adamulrich/CulturalHallLighting/20211202_095547.jpg

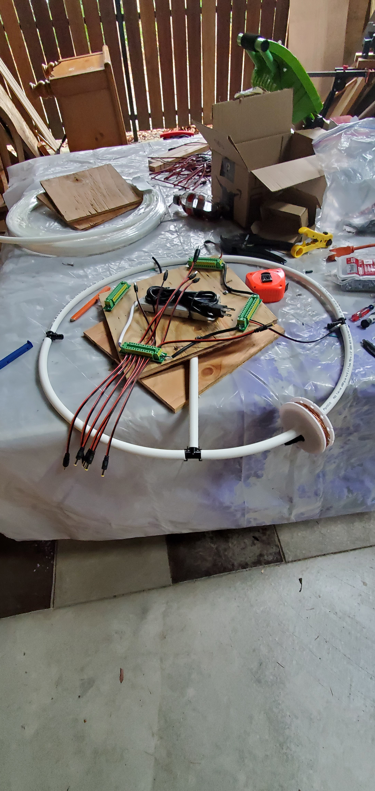
20211202_095547.jpg
