adamulrich/CulturalHallLighting/20211214_210018.jpg

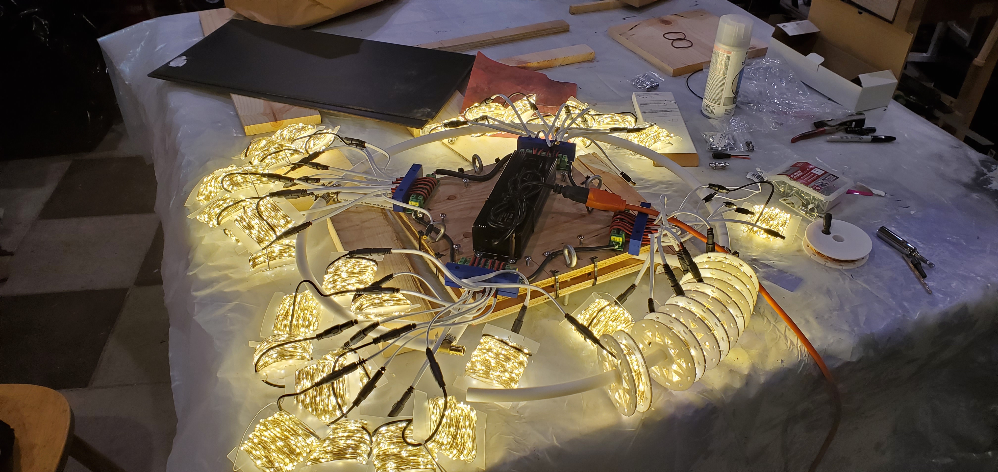
20211214_210018.jpg
