adamulrich/CulturalHallLighting/20211214_210051 (Large).jpg

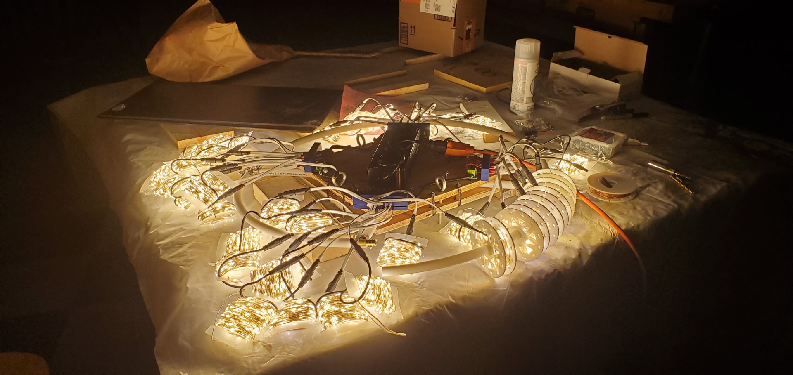
20211214_210051 (Large).jpg
