adamulrich/CulturalHallLighting/IMG_20211204_191200.jpg

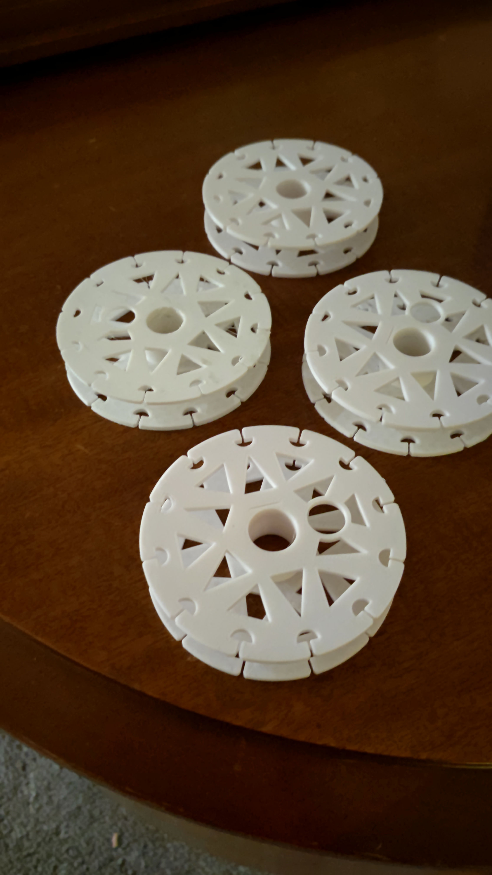
IMG_20211204_191200.jpg
