adamulrich/CulturalHallLighting/IMG_20211204_191239.jpg

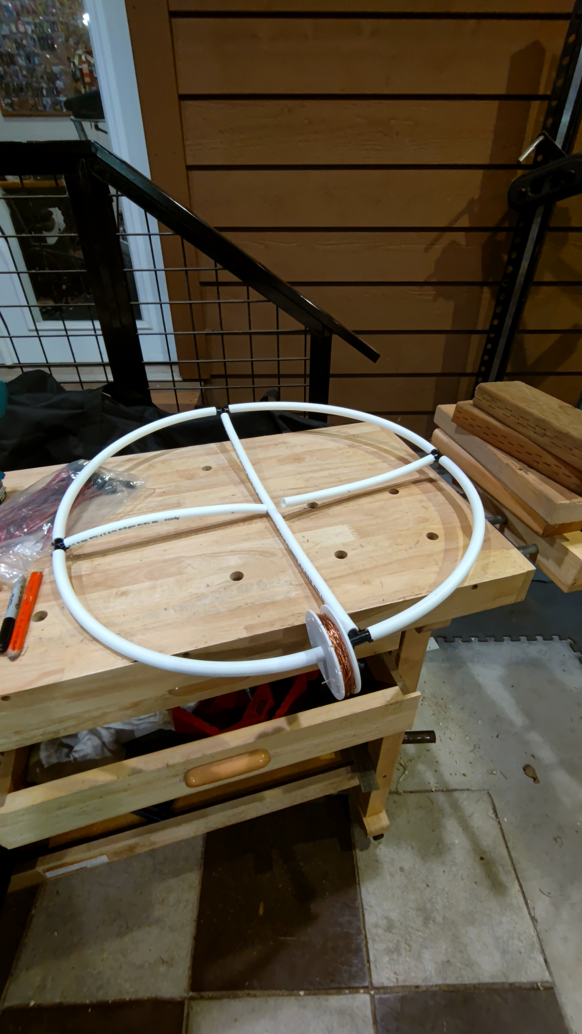
IMG_20211204_191239.jpg
