adamulrich/CulturalHallLighting/IMG_20211204_191243.jpg

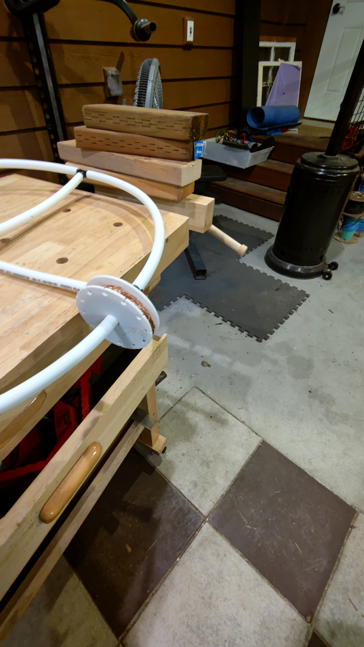
IMG_20211204_191243.jpg
