adamulrich/CulturalHallLighting/IMG_20211204_191250.jpg

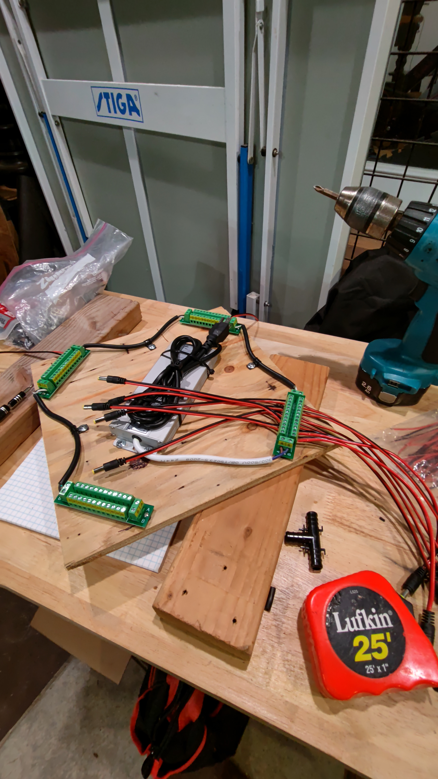
IMG_20211204_191250.jpg
