adamulrich/CulturalHallLighting/IMG_20211204_191428.jpg

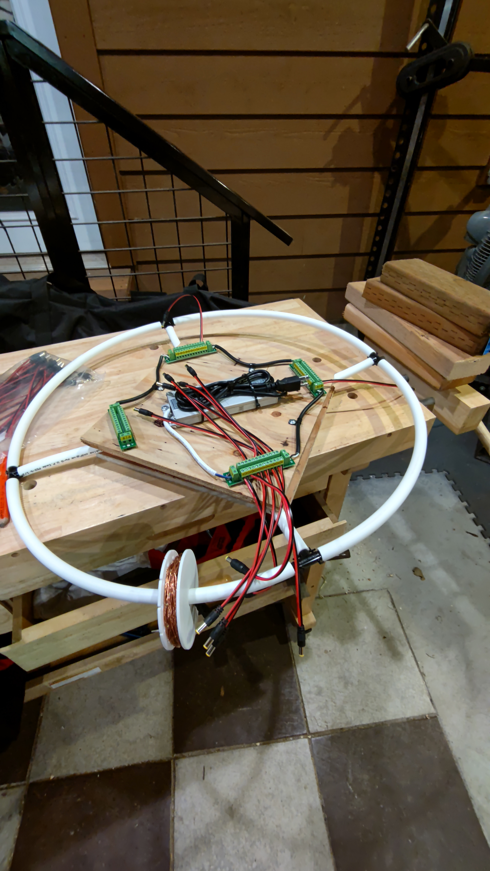
IMG_20211204_191428.jpg
