adamulrich/CulturalHallLighting/IMG_20211204_191507.jpg

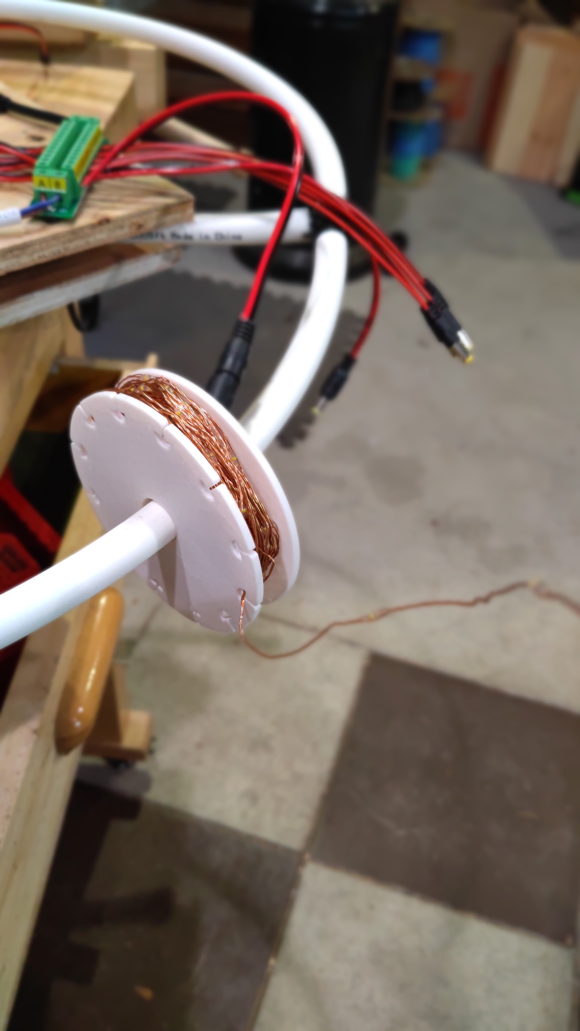
IMG_20211204_191507.jpg
