adamulrich/CulturalHallLighting/IMG_20211204_191512.jpg

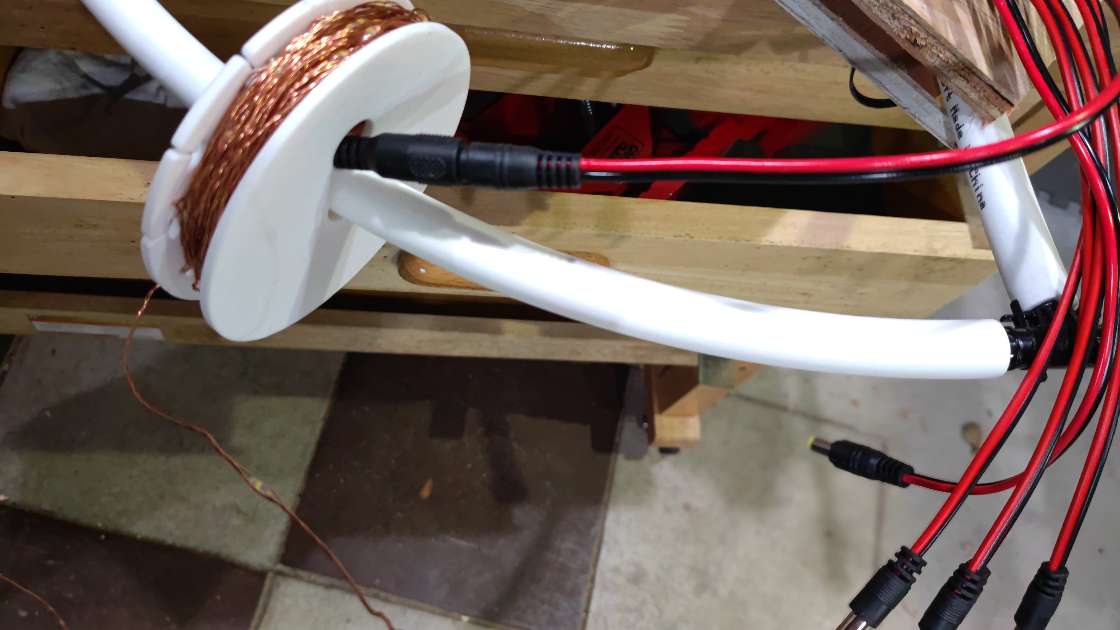
IMG_20211204_191512.jpg
