adamulrich/CulturalHallLighting/IMG_20211207_124333.jpg

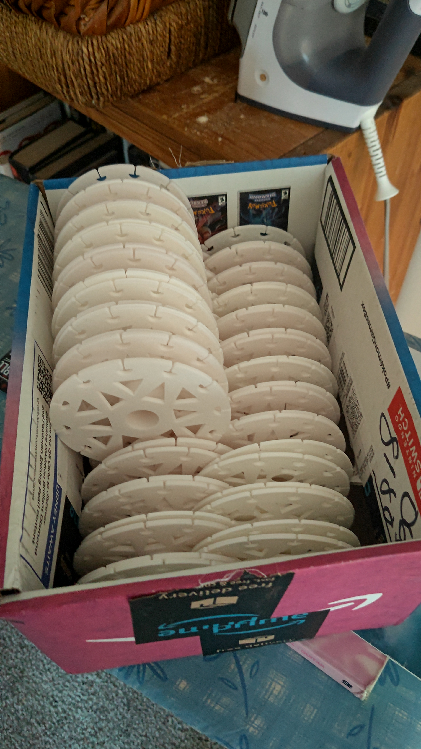
IMG_20211207_124333.jpg
