adamulrich/CulturalHallLighting/IMG_20211210_190347 (Large).jpg

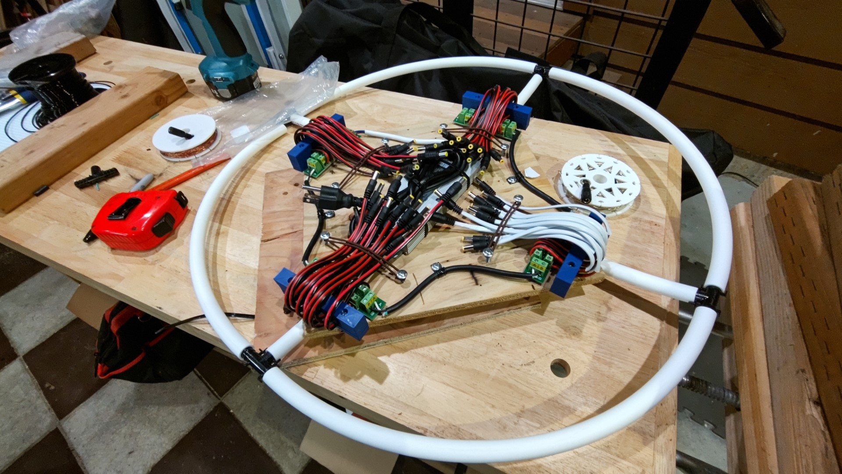
IMG_20211210_190347 (Large).jpg
