adamulrich/CulturalHallLighting/IMG_20211211_223445.jpg

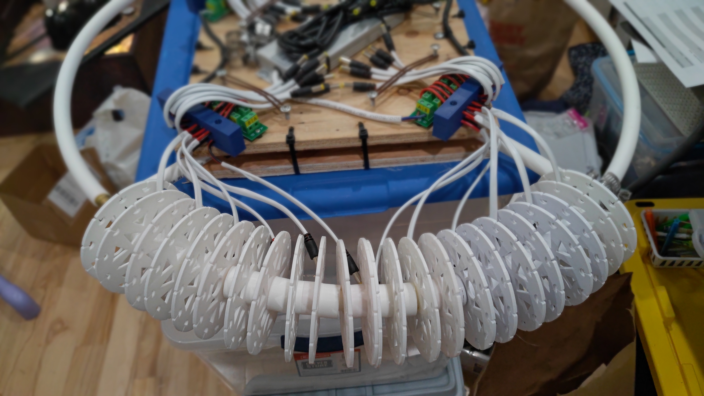
IMG_20211211_223445.jpg
