adamulrich/CulturalHallLighting/IMG_20211211_223448.jpg

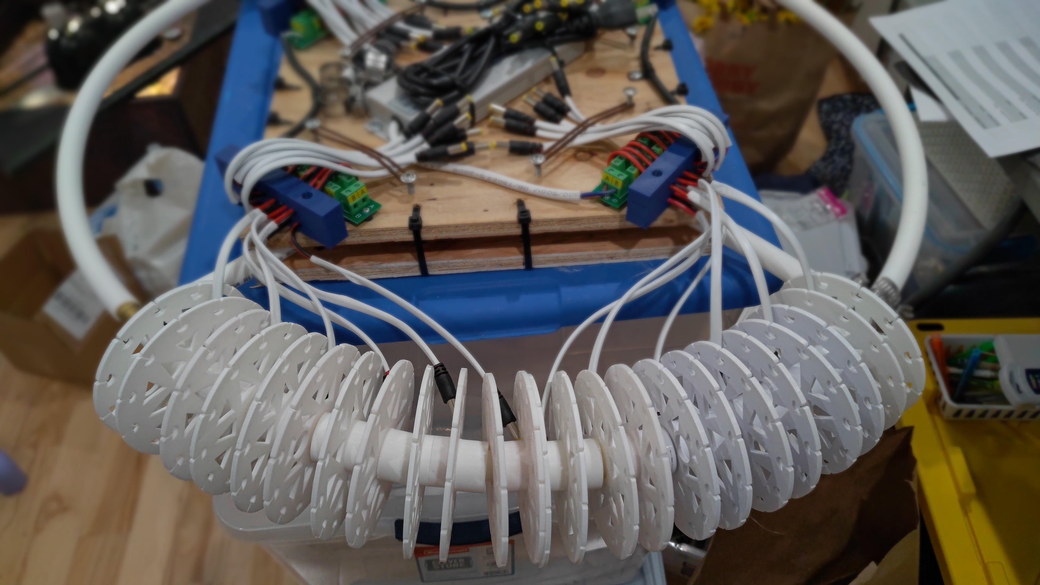
IMG_20211211_223448.jpg
