adamulrich/CulturalHallLighting/IMG_20211211_223452.jpg

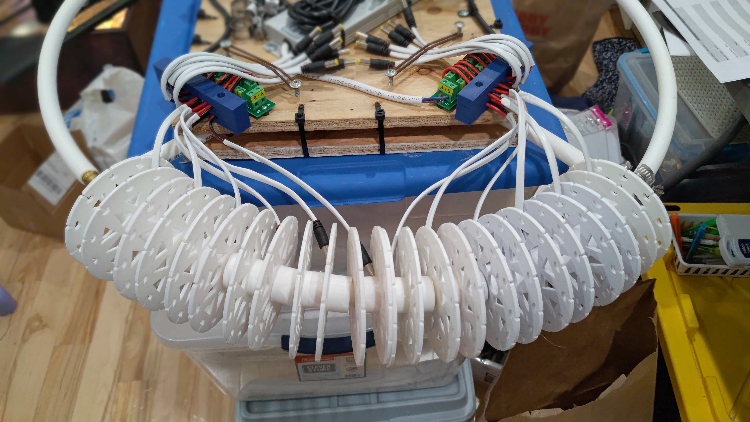
IMG_20211211_223452.jpg
