adamulrich/CulturalHallLighting/IMG_20211211_223614.jpg

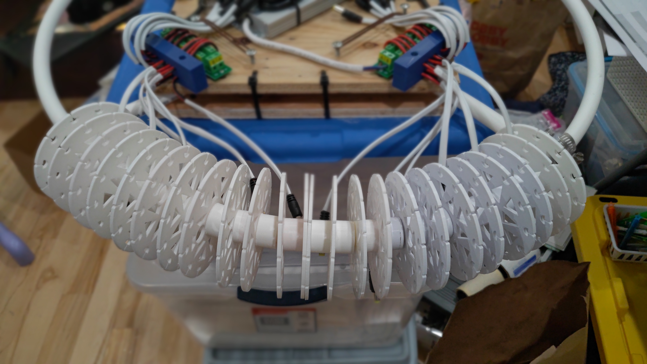
IMG_20211211_223614.jpg
