adamulrich/CulturalHallLighting/IMG_20211215_001636.jpg

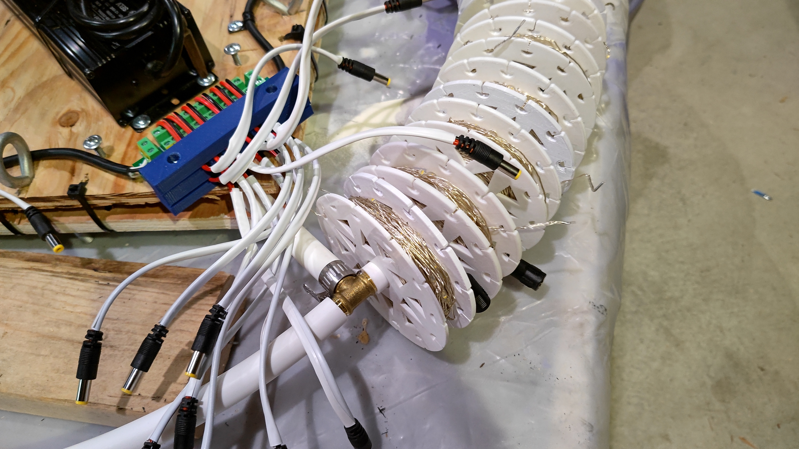
IMG_20211215_001636.jpg
