adamulrich/CulturalHallLighting/IMG_20211219_200439.jpg

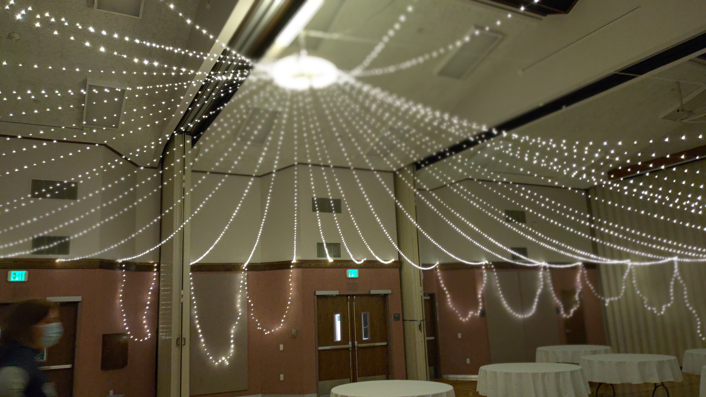
IMG_20211219_200439.jpg
