adamulrich/CulturalHallLighting/IMG_20211219_200453.jpg

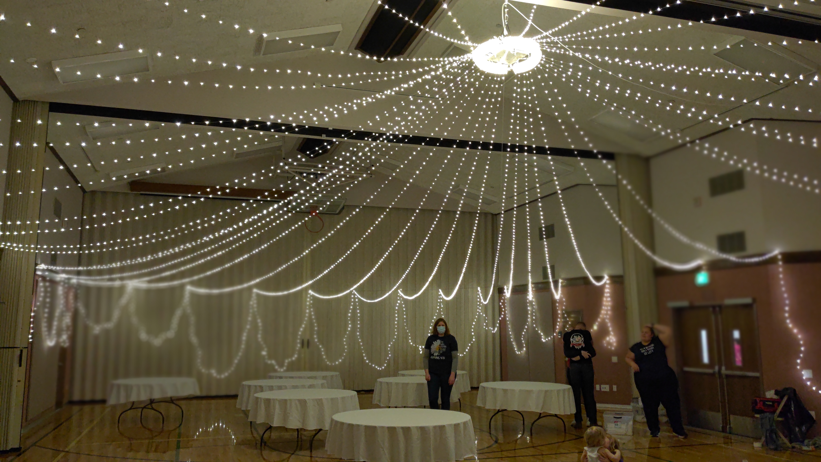
IMG_20211219_200453.jpg
