adamulrich/CulturalHallLighting/IMG_20211219_200454.jpg

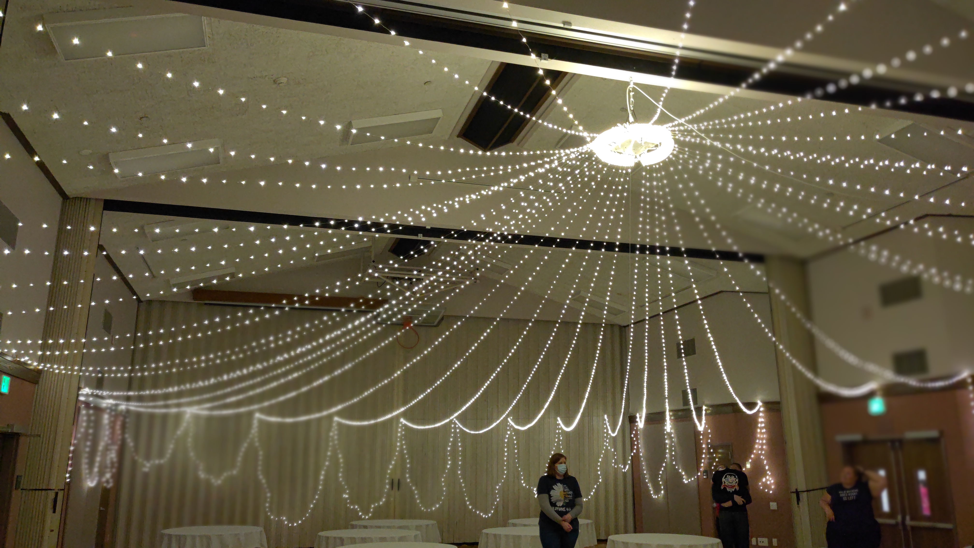
IMG_20211219_200454.jpg
