adamulrich/CulturalHallLighting/IMG_20231211_173214.jpg

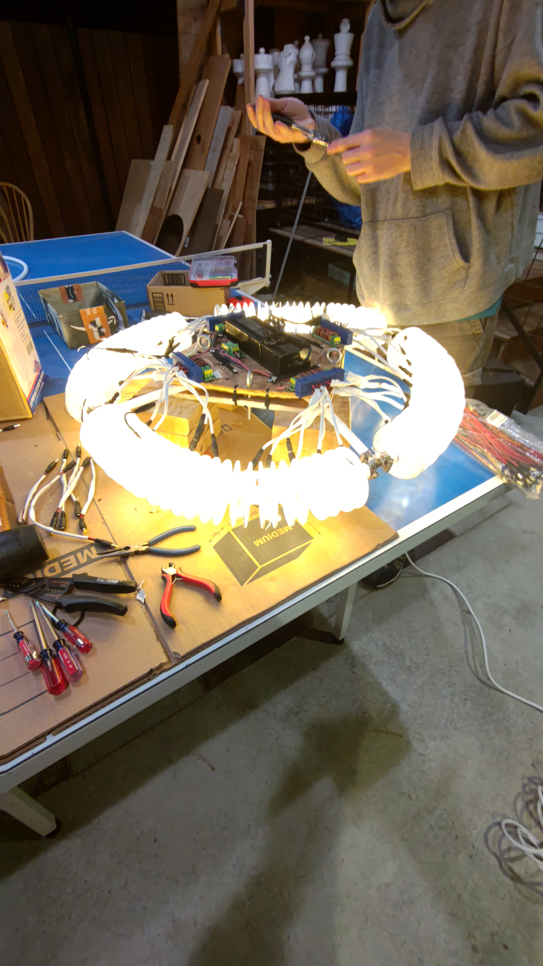
IMG_20231211_173214.jpg
