adamulrich/CulturalHallLighting/IMG_20231214_221152.jpg

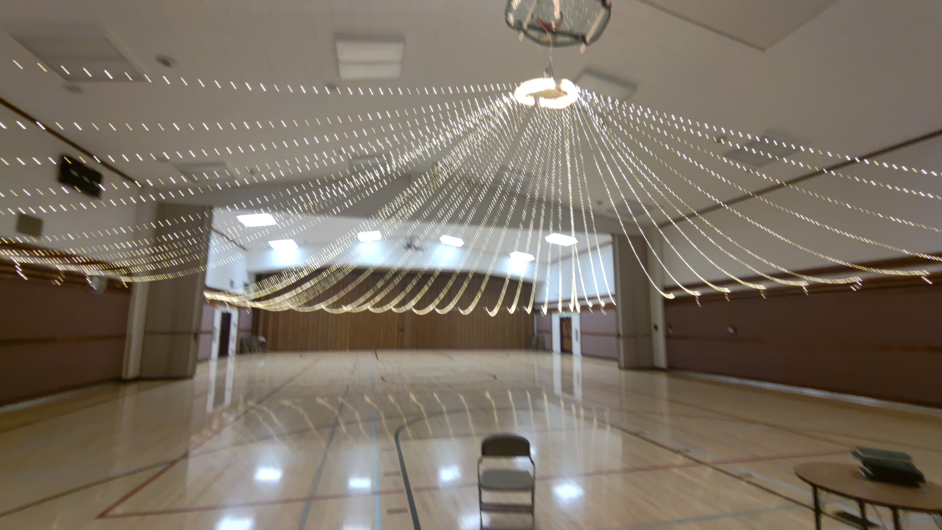
IMG_20231214_221152.jpg
