adamulrich/CulturalHallLighting/IMG_20231214_221206.jpg

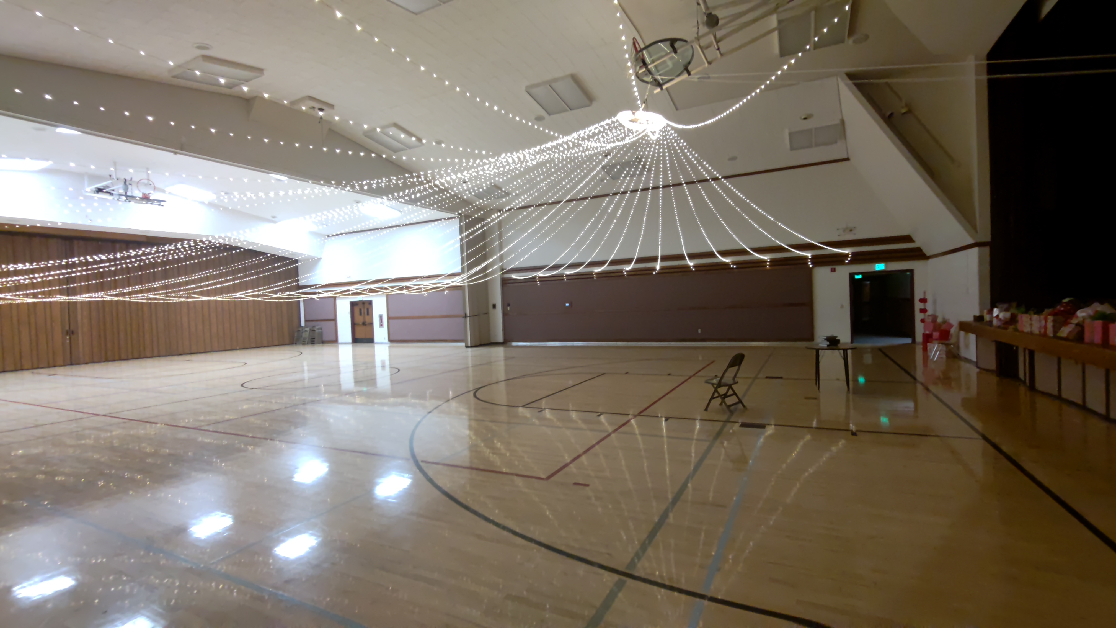
IMG_20231214_221206.jpg
