adamulrich/CulturalHallLighting/IMG_20231215_181741.jpg

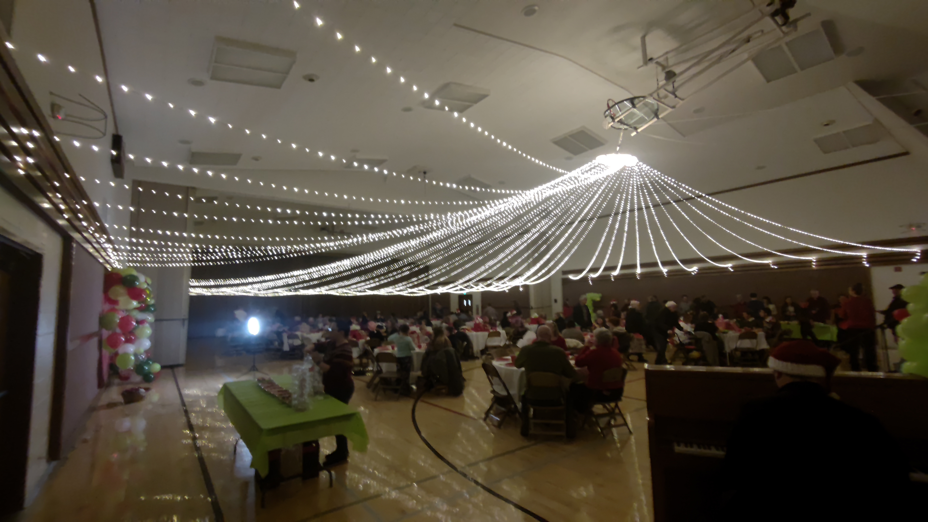
IMG_20231215_181741.jpg
