adamulrich/CulturalHallLighting/IMG_20231215_181755.jpg

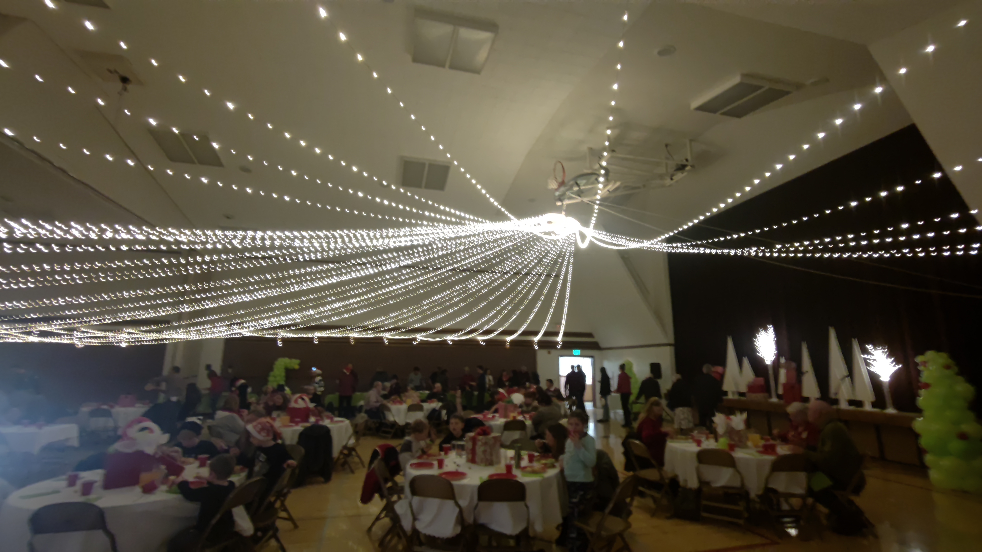
IMG_20231215_181755.jpg
