adamulrich/CulturalHallLighting/IMG_20231216_153002.jpg

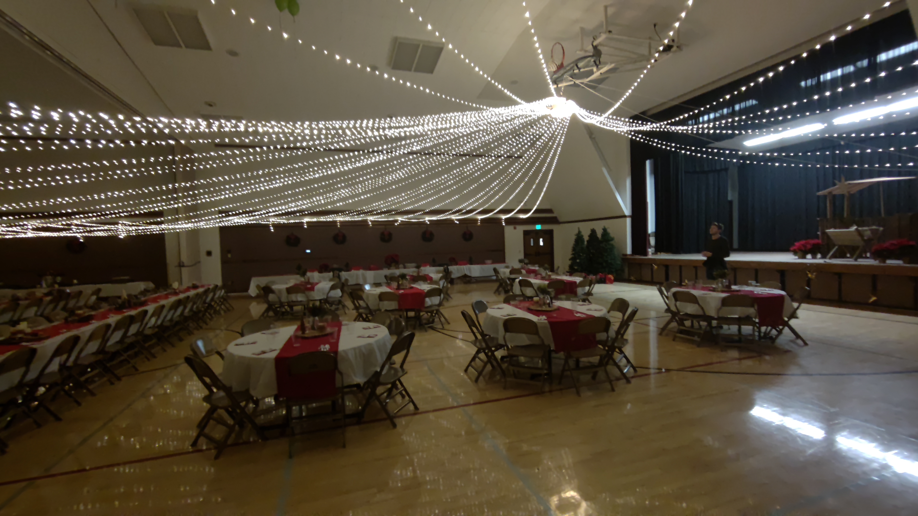
IMG_20231216_153002.jpg
