adamulrich/CulturalHallLighting/IMG_20231216_153027.jpg

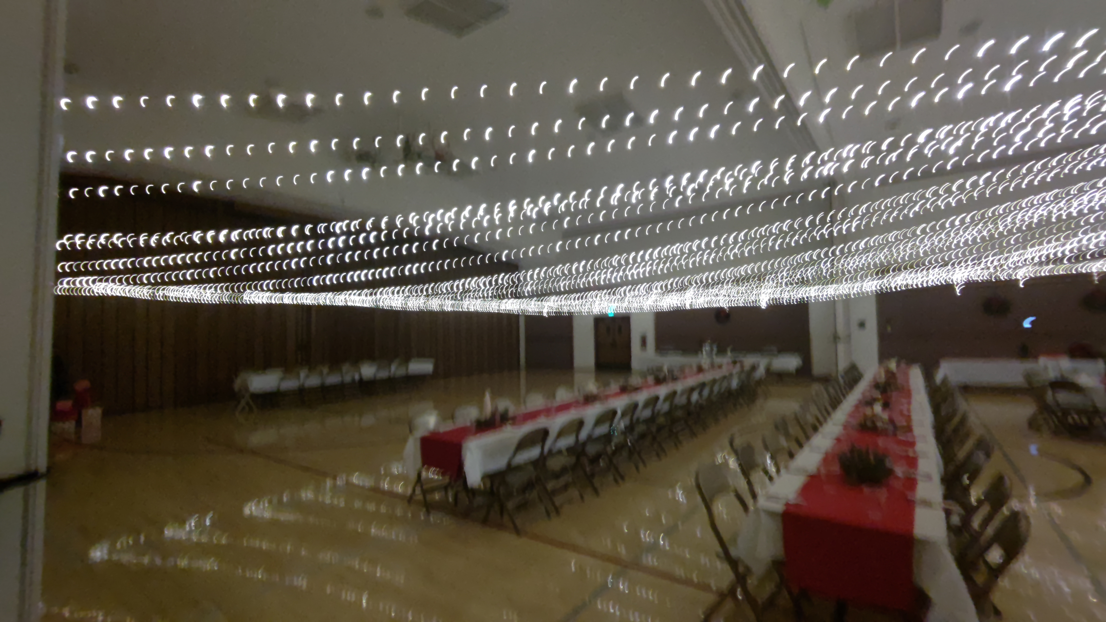
IMG_20231216_153027.jpg
